ZoeGet/OmiPet/Firmware/src/ics43434_mic.cpp

#include "ics43434_mic.h"

//  ICS-43434 I2S 数字麦克风驱动实现 / ICS-43434 I2S digital microphone driver implementation
#include <algorithm>

namespace OmiPetAudio {

//  初始化 ICS-43434 的 I2S 接收配置 / Initialize the ICS-43434 I2S receive configuration
bool Ics43434Mic::begin(uint32_t sampleRateHz, MicChannel channel) {
  if (sampleRateHz == 0U) {
    return false;
  }

  if (initialized_) {
    end();
  }

  sampleRateHz_ = sampleRateHz;
  channel_ = channel;

  //  显式配置旧版 ESP-IDF I2S 接收驱动 / Configure the legacy ESP-IDF I2S RX driver explicitly
  //  避免 Arduino I2SClass 默认引脚和全局回调队列问题 / This avoids Arduino I2SClass default pins and its global callback queue
  i2s_config_t config = {};
  config.mode = static_cast<i2s_mode_t>(I2S_MODE_MASTER | I2S_MODE_RX);
  config.sample_rate = sampleRateHz_;
  config.bits_per_sample = I2S_BITS_PER_SAMPLE_32BIT;
  config.channel_format = I2S_CHANNEL_FMT_RIGHT_LEFT;
  config.communication_format = I2S_COMM_FORMAT_STAND_I2S;
  config.intr_alloc_flags = ESP_INTR_FLAG_LEVEL1;
  config.dma_buf_count = 4;  //  I2S DMA 缓冲区数量 / Number of I2S DMA buffers
  config.dma_buf_len = 128;  //  每个 DMA 缓冲区的采样槽数量 / Slot count in each DMA buffer
  config.use_apll = false;
  config.tx_desc_auto_clear = false;
  config.fixed_mclk = 0;  //  ICS-43434 不使用 MCLK / ICS-43434 does not use MCLK

  const esp_err_t installResult =
      i2s_driver_install(port_, &config, 0, nullptr);
  if (installResult != ESP_OK) {
    initialized_ = false;
    return false;
  }

  i2s_pin_config_t pins = {};
  pins.mck_io_num = I2S_PIN_NO_CHANGE;  //  不输出 MCLK / Do not output MCLK
  pins.bck_io_num = kMicSckPin;  //  连接麦克风 SCK/BCLK / Connect to microphone SCK/BCLK
  pins.ws_io_num = kMicWsPin;  //  连接麦克风 WS/LRCLK / Connect to microphone WS/LRCLK
  pins.data_out_num = I2S_PIN_NO_CHANGE;  //  仅使用接收方向，不输出数据 / RX only, no data output
  pins.data_in_num = kMicSdPin;  //  连接麦克风 SD / Connect to microphone SD

  const esp_err_t pinResult = i2s_set_pin(port_, &pins);
  if (pinResult != ESP_OK) {
    i2s_driver_uninstall(port_);
    initialized_ = false;
    return false;
  }

  initialized_ = true;
  return true;
}

//  卸载 I2S 驱动并释放麦克风接收资源 / Uninstall the I2S driver and release microphone resources
void Ics43434Mic::end() {
  if (!initialized_) {
    return;
  }

  i2s_driver_uninstall(port_);
  initialized_ = false;
}

//  查询 I2S 麦克风是否已经初始化 / Check whether the I2S microphone is initialized
bool Ics43434Mic::initialized() const {
  return initialized_;
}

//  读取原始 I2S 采样槽，并返回实际读取的字数 / Read raw I2S sample slots and return the number of words read
size_t Ics43434Mic::readRawWords(int32_t* buffer, size_t wordCount) {
  if (!initialized_ || buffer == nullptr || wordCount == 0U) {
    return 0;
  }

  const size_t requestedBytes = wordCount * sizeof(int32_t);
  size_t bytesRead = 0;
  const esp_err_t result =
      i2s_read(port_, buffer, requestedBytes, &bytesRead, pdMS_TO_TICKS(20));
  if (result != ESP_OK || bytesRead == 0U) {
    return 0;
  }

  return std::min(bytesRead / sizeof(int32_t), wordCount);
}

//  返回当前使用的麦克风左右声道槽 / Return the selected microphone channel slot
MicChannel Ics43434Mic::channel() const {
  return channel_;
}

//  返回当前 I2S 采样率 / Return the active I2S sample rate
uint32_t Ics43434Mic::sampleRateHz() const {
  return sampleRateHz_;
}

Ics43434Mic microphone;

}  //  OmiPetAudio 命名空间 / OmiPetAudio namespace
